gklyne/monotype_tape_reader/Notes/Decoder colors.jpg

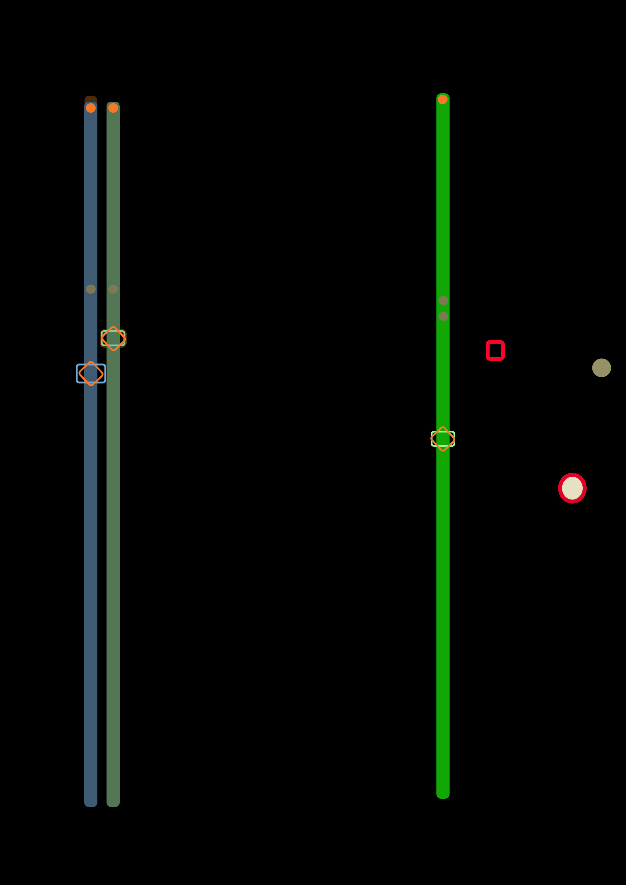
Notes/Decoder colors.jpg
