gklyne/monotype_tape_reader/Notes/DHOxSS-poster/20220516-DHOxSS-Monotype-Reader-poster.graffle/image12.tiff

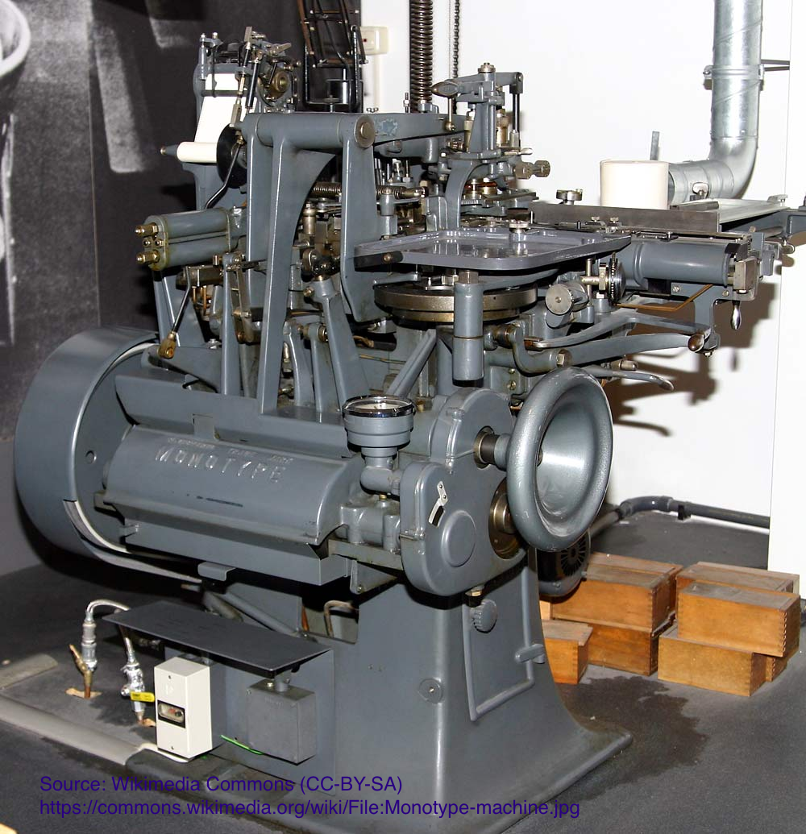
Notes/DHOxSS-poster/20220516-DHOxSS-Monotype-Reader-poster.graffle/image12.tiff
