gklyne/monotype_tape_reader/Notes/DHOxSS-poster/20220516-DHOxSS-Monotype-Reader-poster.graffle/image15.jpeg

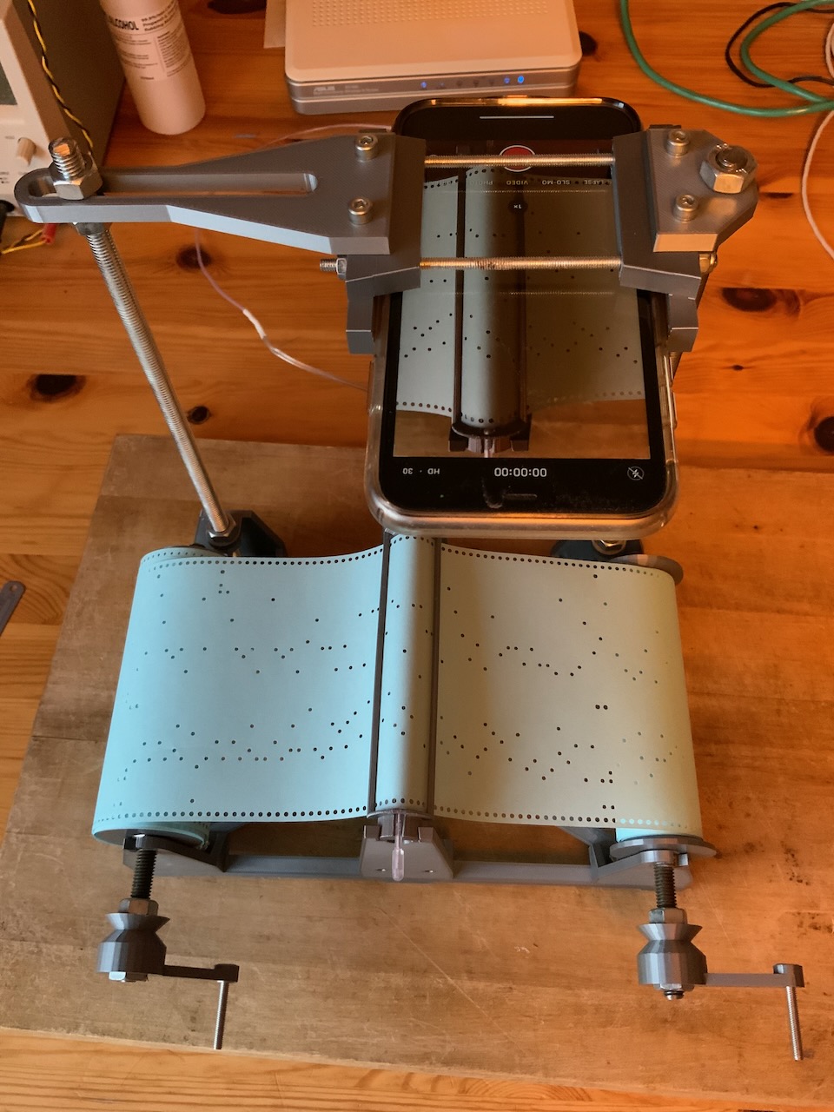
Notes/DHOxSS-poster/20220516-DHOxSS-Monotype-Reader-poster.graffle/image15.jpeg
