gklyne/monotype_tape_reader/Notes/DHOxSS-poster/20220516-DHOxSS-Monotype-Reader-poster.graffle/image16.png

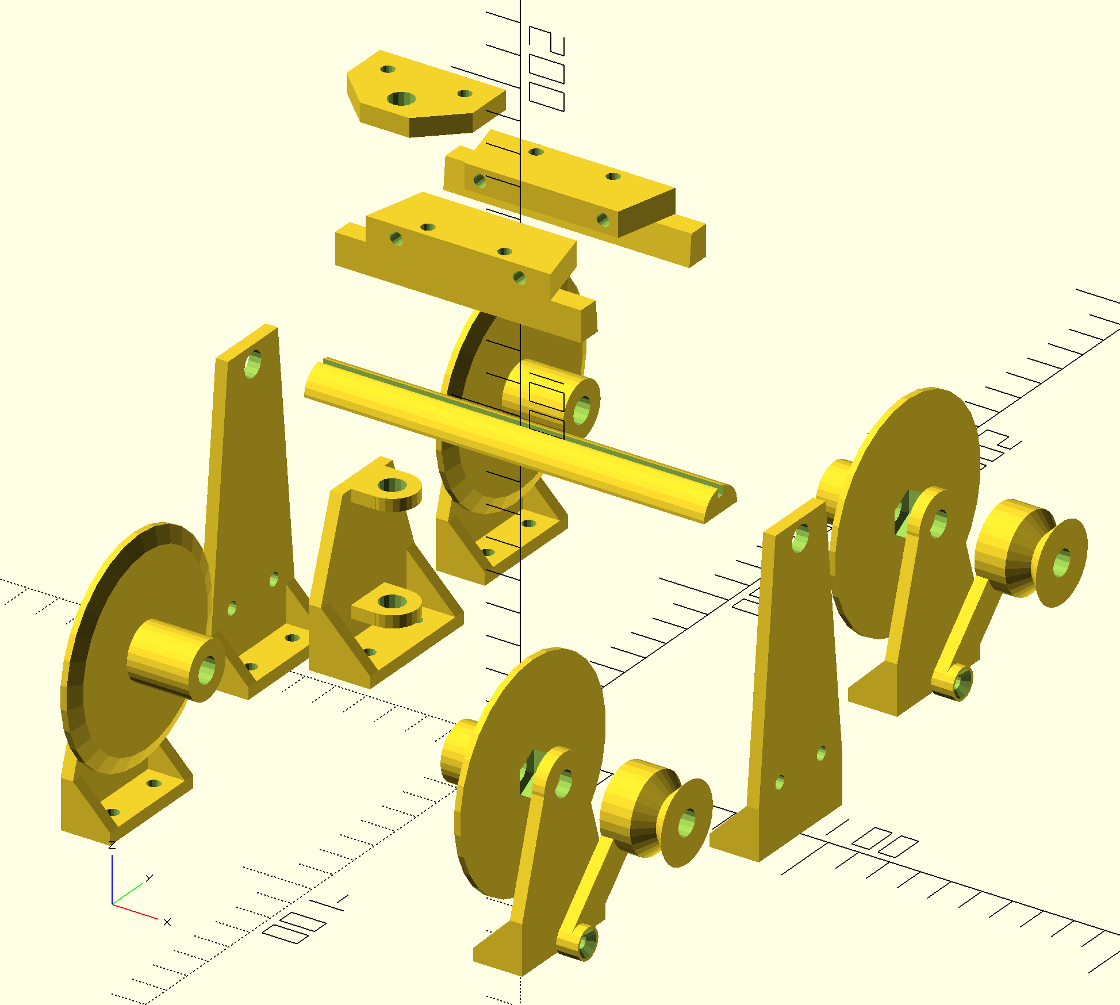
Notes/DHOxSS-poster/20220516-DHOxSS-Monotype-Reader-poster.graffle/image16.png
