gklyne/monotype_tape_reader/Notes/Monotype_tape_reader_Mk3.jpeg

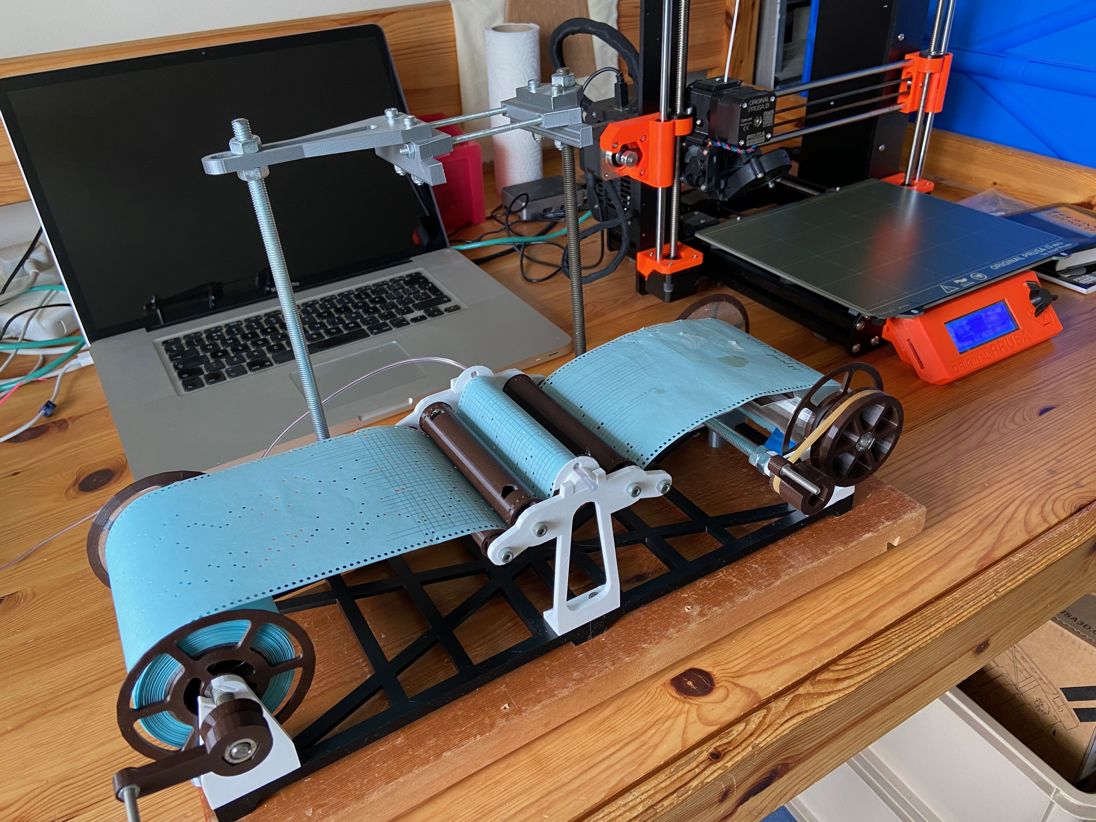
Notes/Monotype_tape_reader_Mk3.jpeg
