gklyne/monotype_tape_reader/Monocaster-assembly-exploded.jpg

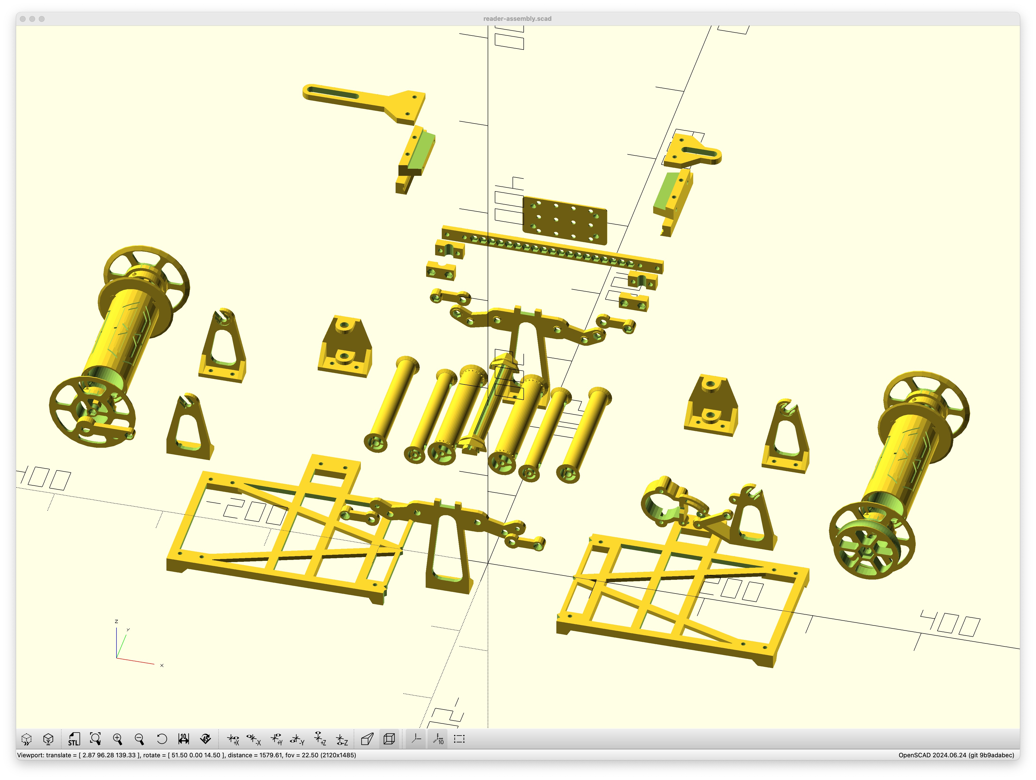
Monocaster-assembly-exploded.jpg
